lukasznowarkiewicz/DeafAlDer/imagesAndPhotos/altium/alarmClockScreen_pcb_bottom.JPG

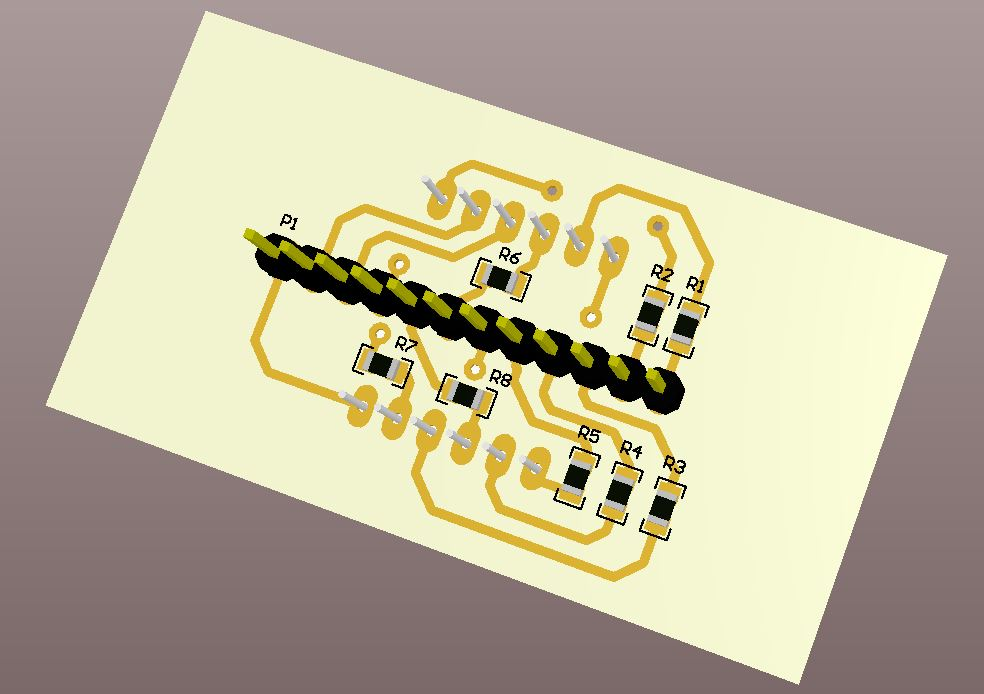
imagesAndPhotos/altium/alarmClockScreen_pcb_bottom.JPG
