lukasznowarkiewicz/DeafAlDer/imagesAndPhotos/altium/alarmClockScreen_pcb_top.JPG

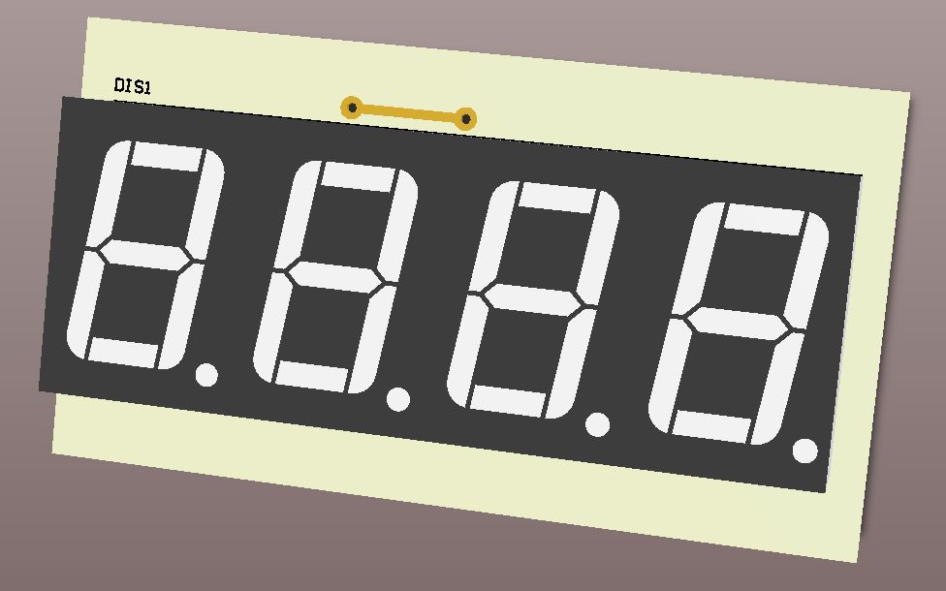
imagesAndPhotos/altium/alarmClockScreen_pcb_top.JPG
