lukasznowarkiewicz/DeafAlDer/imagesAndPhotos/altium/chadDetector_bottom.JPG

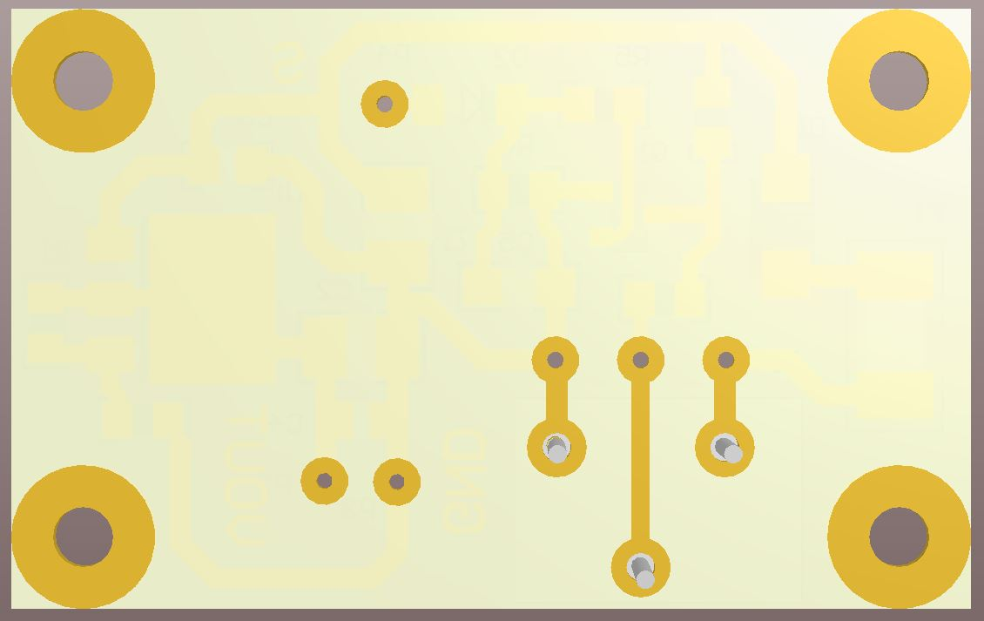
imagesAndPhotos/altium/chadDetector_bottom.JPG
