lukasznowarkiewicz/DeafAlDer/imagesAndPhotos/altium/chadDetector_pcb.JPG

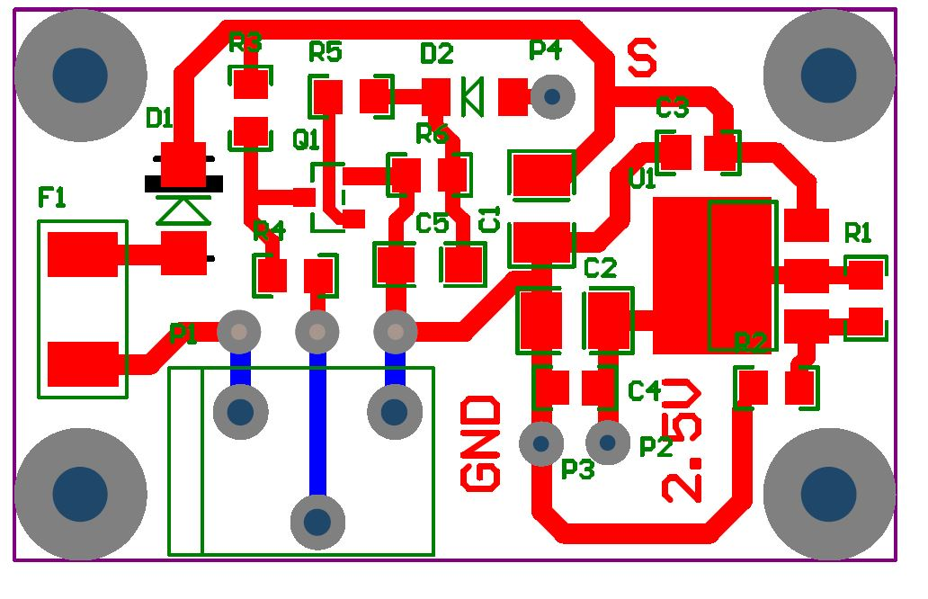
imagesAndPhotos/altium/chadDetector_pcb.JPG
