lukasznowarkiewicz/DeafAlDer/imagesAndPhotos/altium/chadDetector_top.JPG

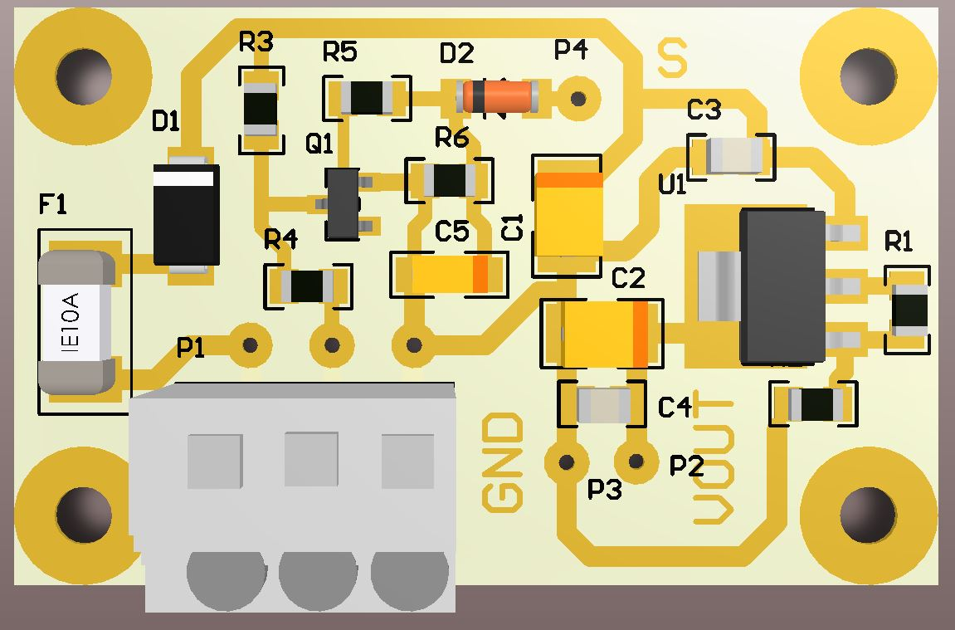
imagesAndPhotos/altium/chadDetector_top.JPG
