lukasznowarkiewicz/DeafAlDer/imagesAndPhotos/altium/ringingPhoneDetector_bottom.JPG

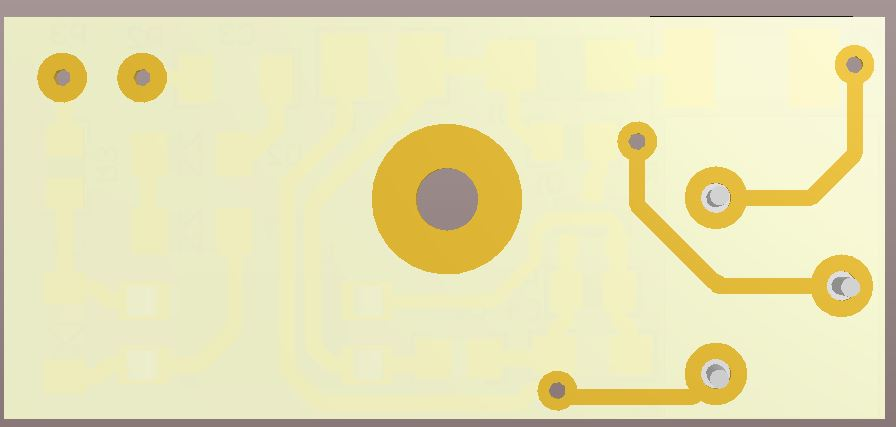
imagesAndPhotos/altium/ringingPhoneDetector_bottom.JPG
