lukasznowarkiewicz/DeafAlDer/imagesAndPhotos/altium/ringingPhoneDetector_pcb.JPG

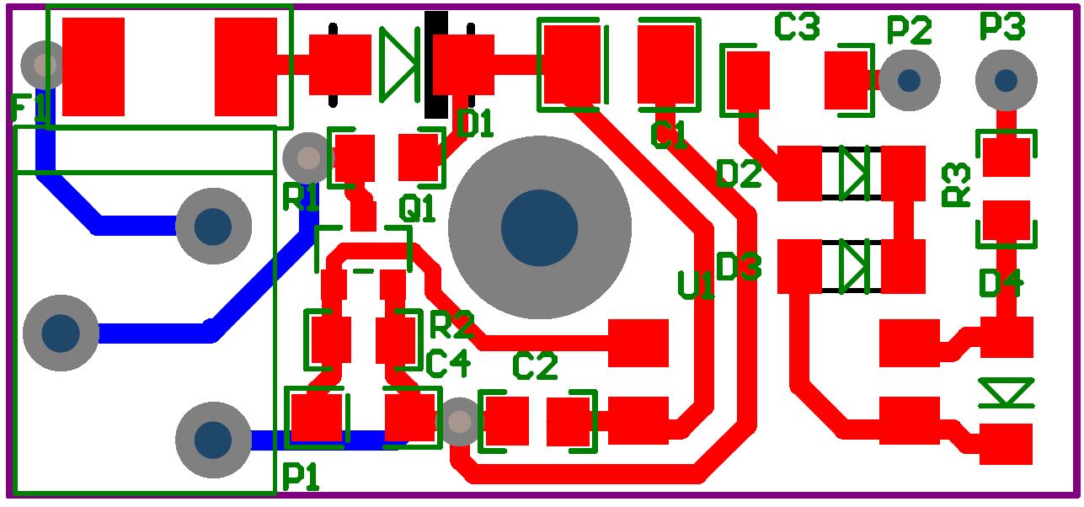
imagesAndPhotos/altium/ringingPhoneDetector_pcb.JPG
