lukasznowarkiewicz/DeafAlDer/imagesAndPhotos/altium/ringingPhoneDetector_sch.JPG

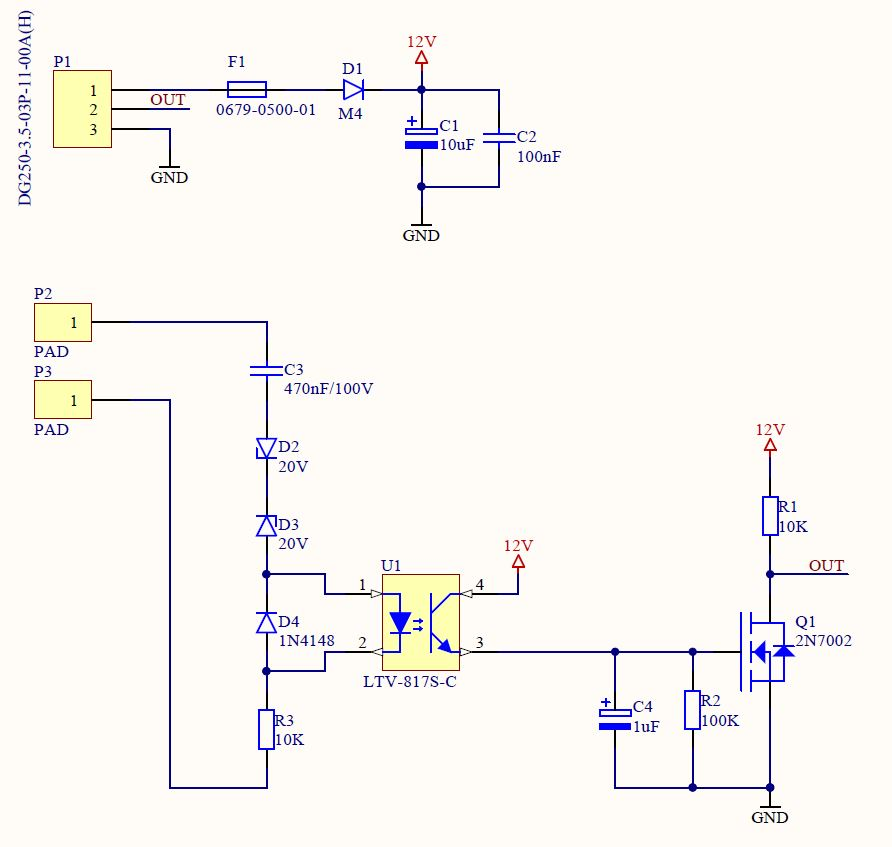
imagesAndPhotos/altium/ringingPhoneDetector_sch.JPG
