lukasznowarkiewicz/DeafAlDer/imagesAndPhotos/altium/ringingPhoneDetector_top.JPG

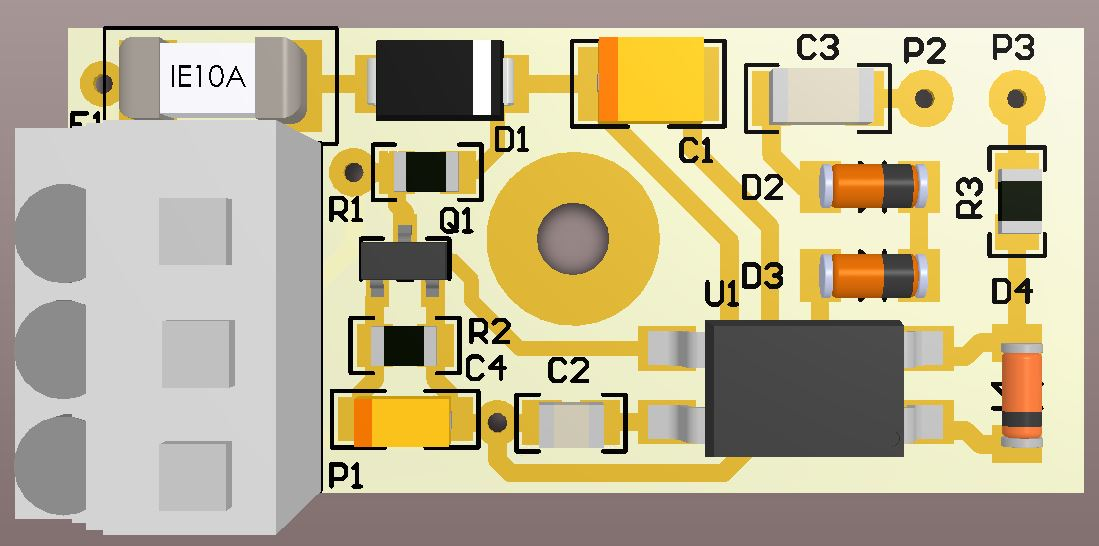
imagesAndPhotos/altium/ringingPhoneDetector_top.JPG
