lukasznowarkiewicz/DeafAlDer/imagesAndPhotos/altium/timer_bottom.JPG

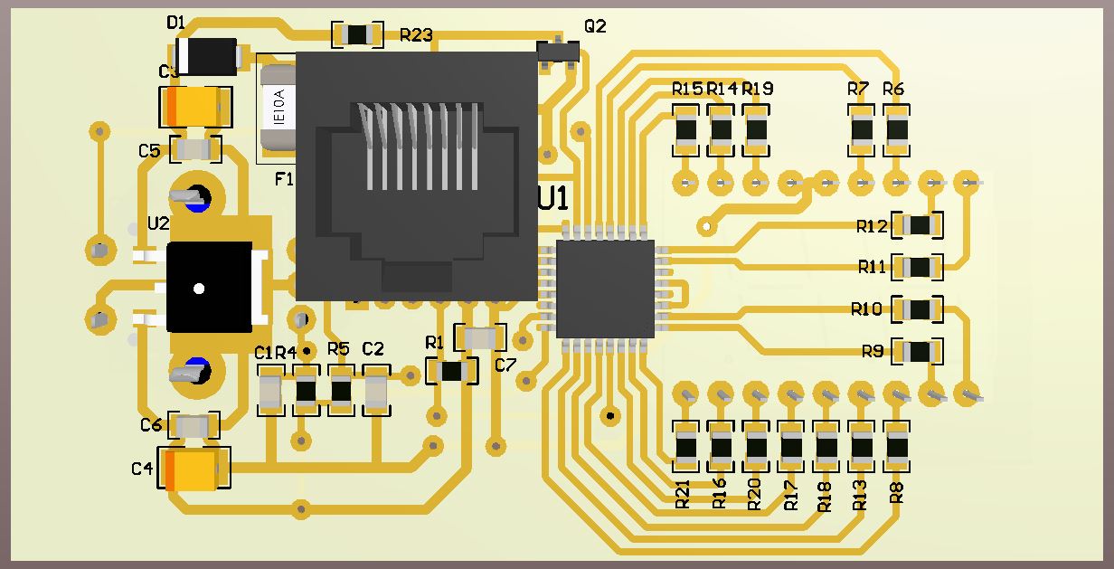
imagesAndPhotos/altium/timer_bottom.JPG
