lukasznowarkiewicz/DeafAlDer/imagesAndPhotos/doorbell1.JPG

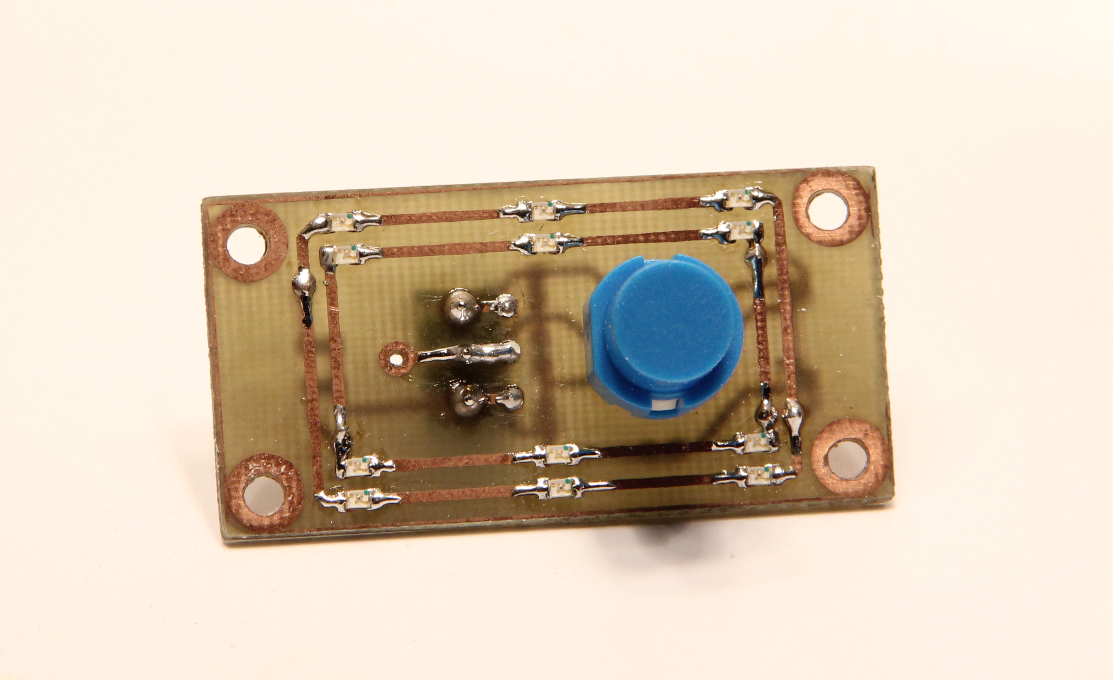
imagesAndPhotos/doorbell1.JPG
