lukasznowarkiewicz/DeafAlDer/imagesAndPhotos/doorbell2.JPG

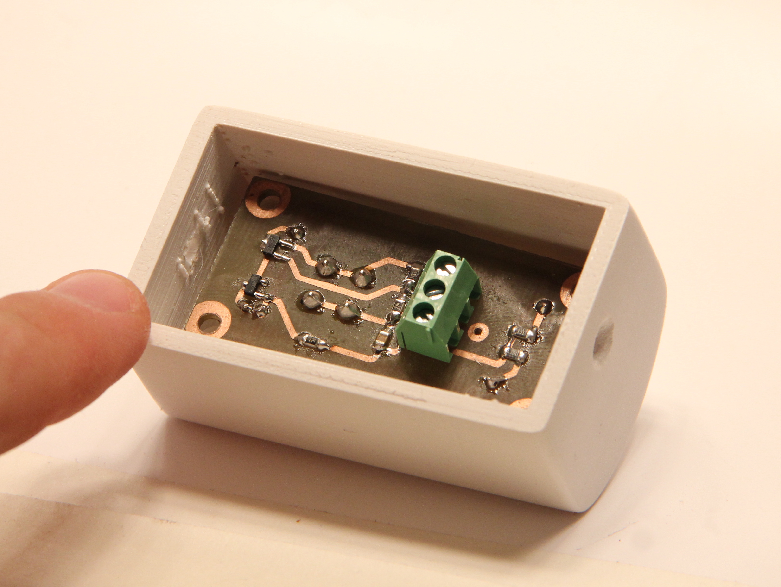
imagesAndPhotos/doorbell2.JPG
