lukasznowarkiewicz/DeafAlDer/imagesAndPhotos/doorbell3.JPG

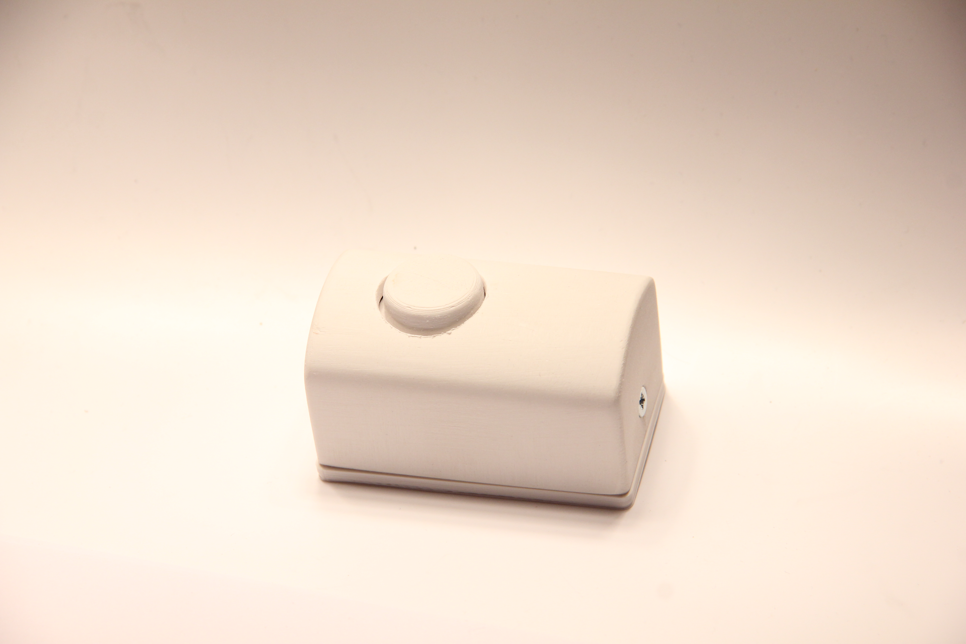
imagesAndPhotos/doorbell3.JPG
