lukasznowarkiewicz/DeafAlDer/imagesAndPhotos/PCB_preparation_3.JPG

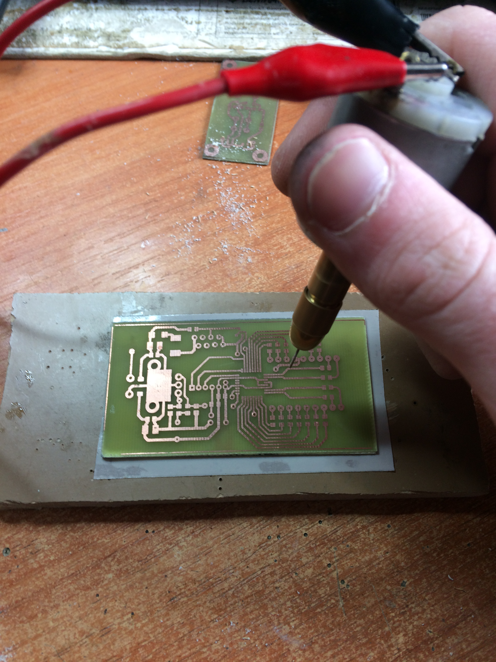
imagesAndPhotos/PCB_preparation_3.JPG
