lukasznowarkiewicz/DeafAlDer/imagesAndPhotos/PCB_preparation_4.JPG

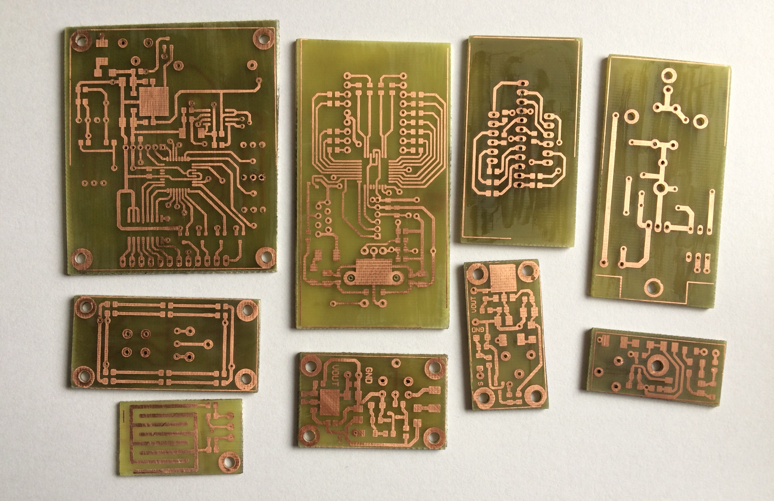
imagesAndPhotos/PCB_preparation_4.JPG
