lukasznowarkiewicz/DeafAlDer/imagesAndPhotos/smokeDetector.JPG

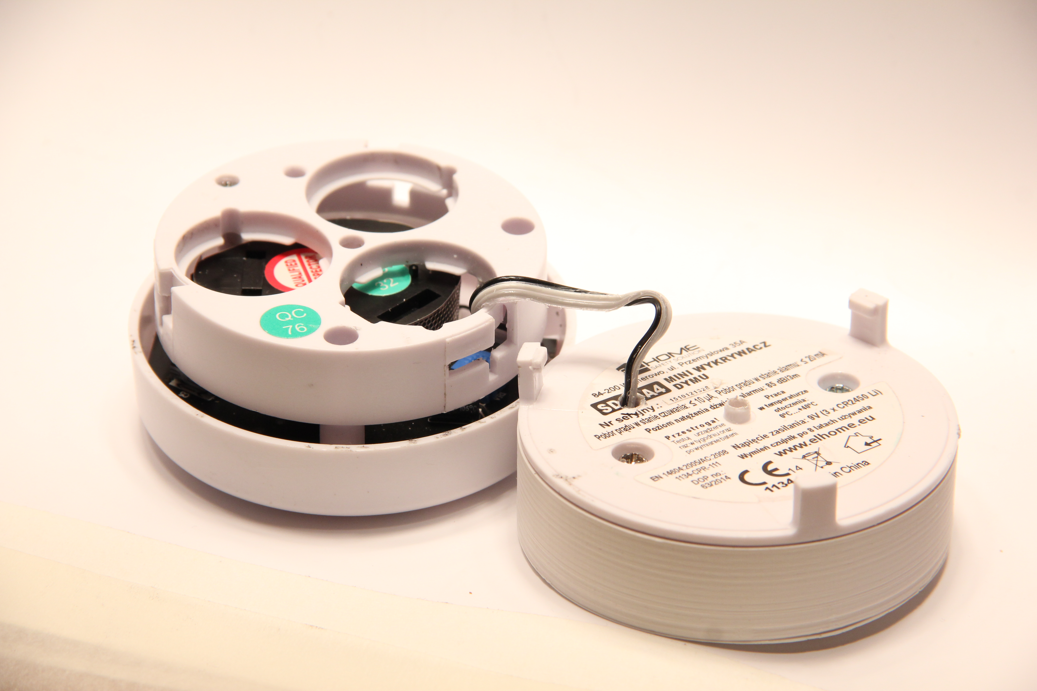
imagesAndPhotos/smokeDetector.JPG
