lukasznowarkiewicz/DeafAlDer/imagesAndPhotos/timer1.JPG

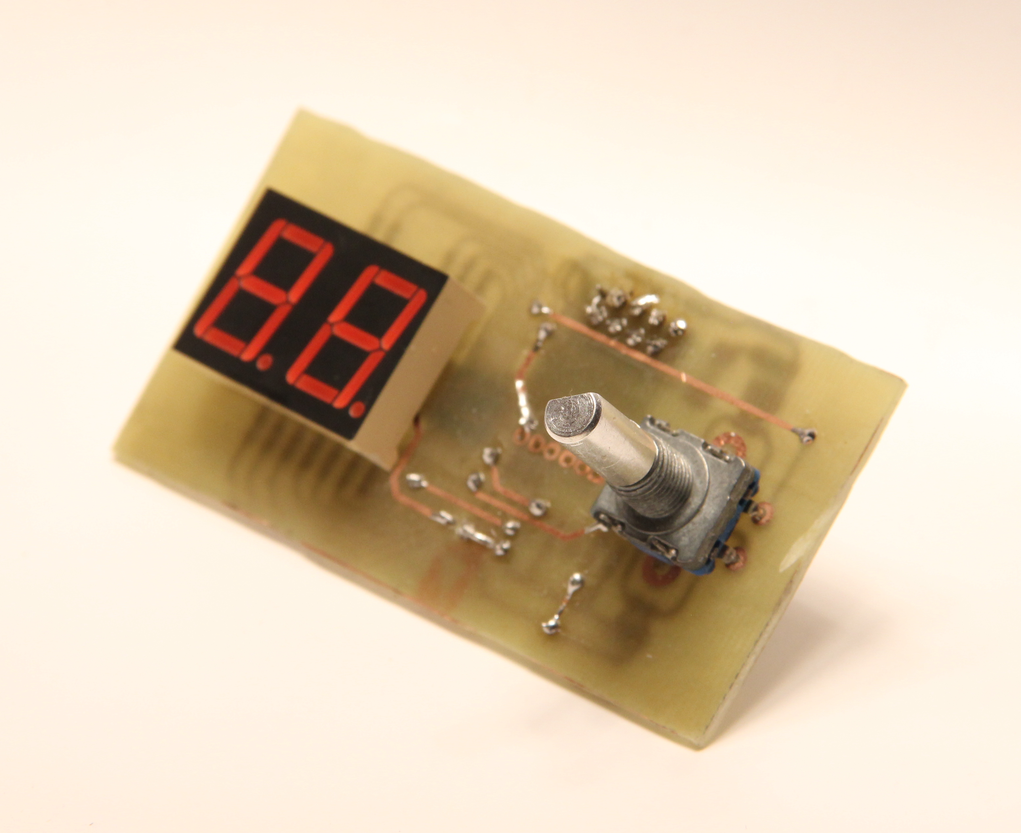
imagesAndPhotos/timer1.JPG
