lukasznowarkiewicz/DeafAlDer/imagesAndPhotos/trophy.JPG

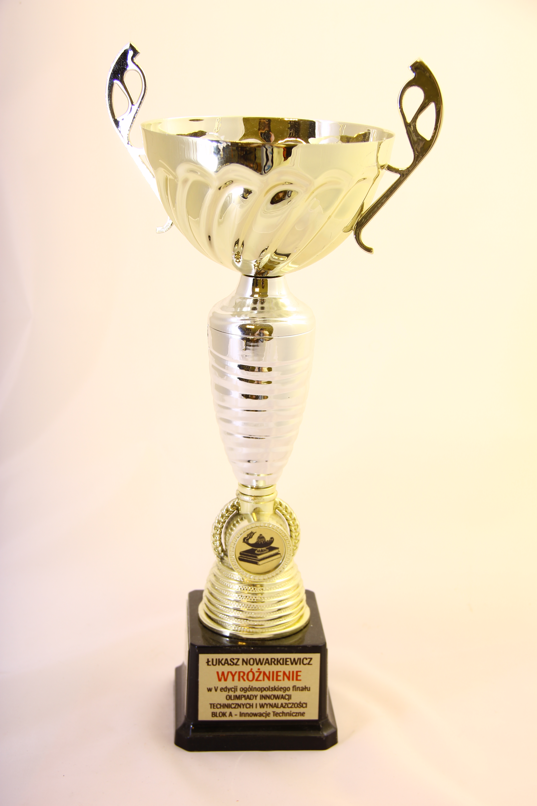
imagesAndPhotos/trophy.JPG
