lukasznowarkiewicz/DeafAlDer/hardware-mechanical/timer/obudowa - timer- back V2.stl

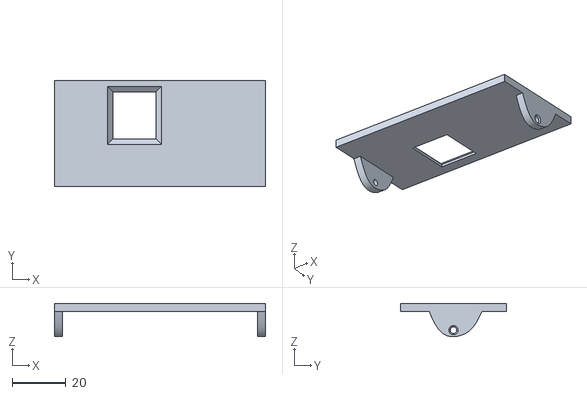
[picture p72: CAD file, 2024-03-28]
hardware-mechanical/timer/obudowa - timer- back V2.stl
78.5 x 39.5 x 12.4
