lukasznowarkiewicz/DeafAlDer/hardware-mechanical/alarmClock/obudowa - budzik v7 plexi.stl

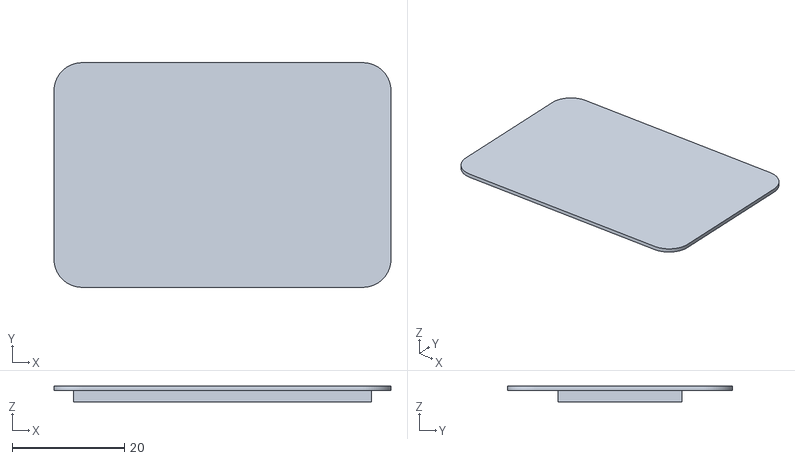
[picture p73: CAD file, 2024-03-28]
hardware-mechanical/alarmClock/obudowa - budzik v7 plexi.stl
60.0 x 40.0 x 2.80
