lukasznowarkiewicz/DeafAlDer/hardware-mechanical/doorbell/guzik.stl

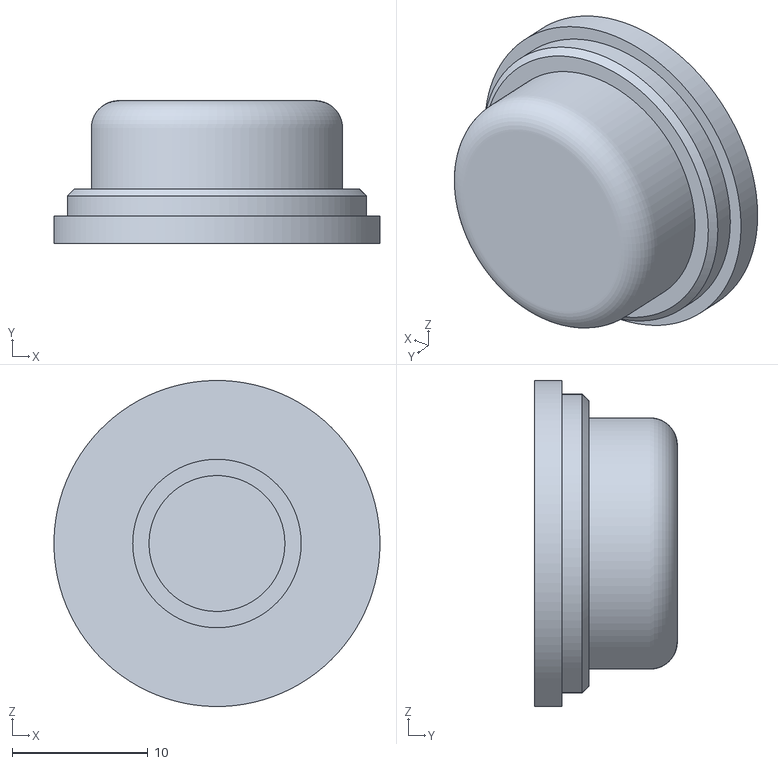
[picture p74: CAD file, 2024-03-28]
hardware-mechanical/doorbell/guzik.stl
24.0 x 10.5 x 24.0
