lukasznowarkiewicz/DeafAlDer/hardware-mechanical/namePlate/tabliczka tworcy i opiekun boki skrzynki.stl

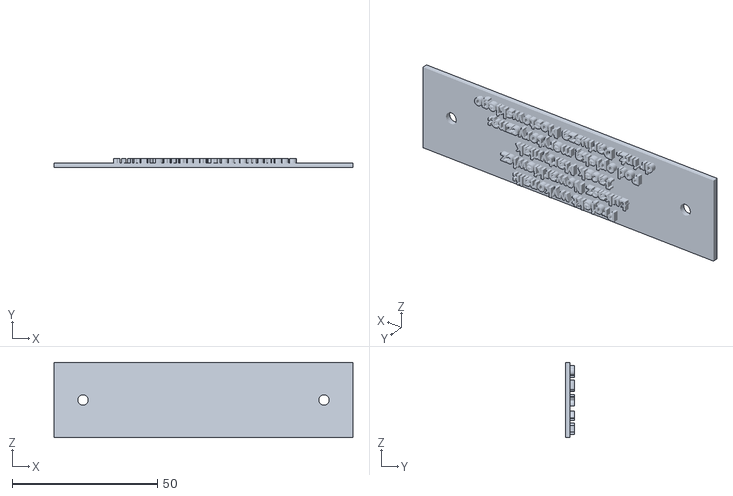
[picture p75: CAD file, 2024-03-28]
hardware-mechanical/namePlate/tabliczka tworcy i opiekun boki skrzynki.stl
103.0 x 3.20 x 26.0
