lukasznowarkiewicz/DeafAlDer/hardware-mechanical/timer/wysw trans v2.stl

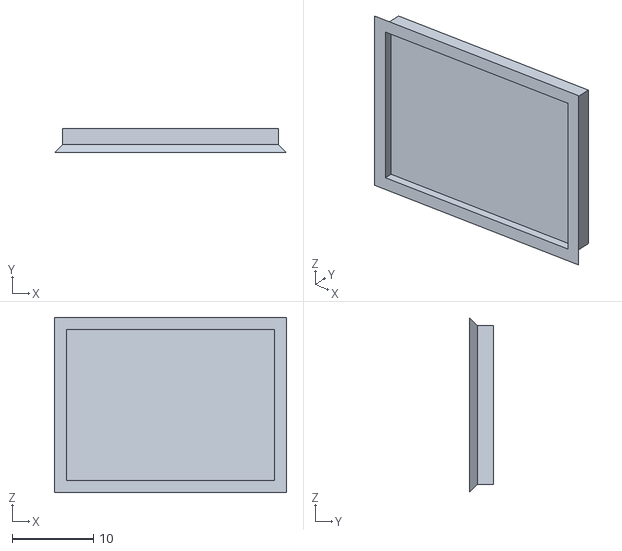
[picture p76: CAD file, 2024-03-28]
hardware-mechanical/timer/wysw trans v2.stl
28.6 x 3.00 x 21.6
