lukasznowarkiewicz/DeafAlDer/hardware-mechanical/doorbell/obudowa - dzwonek- tyl mocowanie do sciany.stl

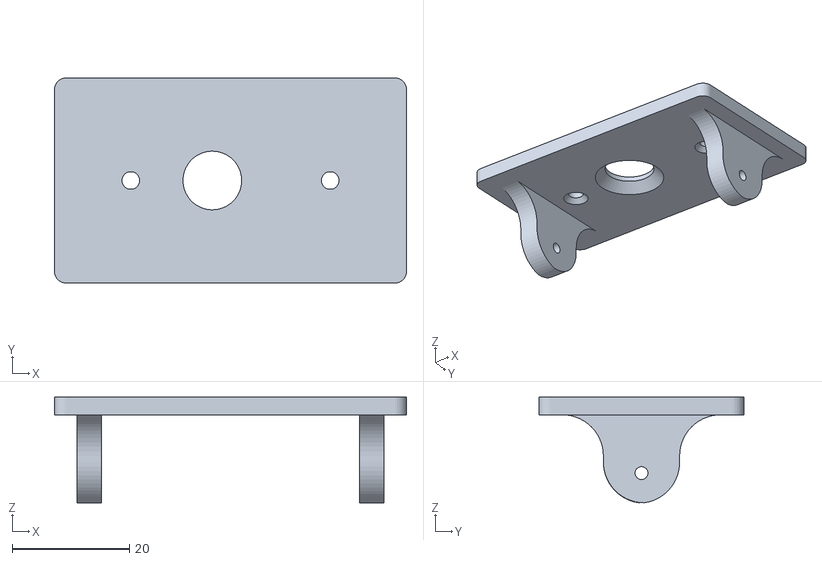
[picture p77: CAD file, 2024-03-28]
hardware-mechanical/doorbell/obudowa - dzwonek- tyl mocowanie do sciany.stl
60.0 x 35.0 x 18.0
