lukasznowarkiewicz/DeafAlDer/hardware-mechanical/namePlate/tabliczka z autorami i opiekunem na przod 170 x 50.stl

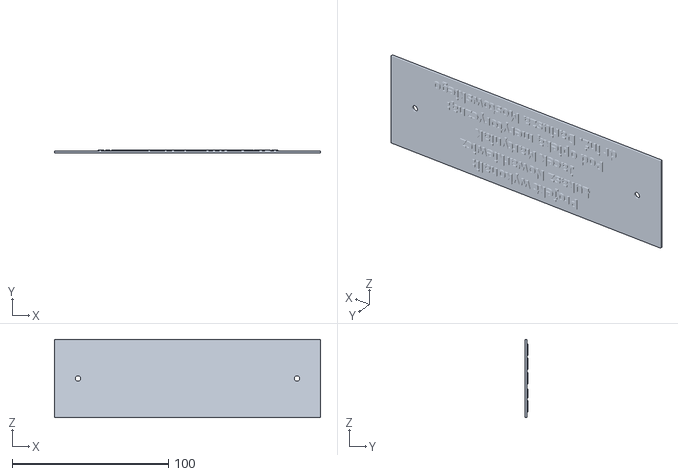
[picture p78: CAD file, 2024-03-28]
hardware-mechanical/namePlate/tabliczka z autorami i opiekunem na przod 170 x 50.stl
170.0 x 2.00 x 50.0
