lukasznowarkiewicz/DeafAlDer/hardware-mechanical/alarmClock/obudowa - budzik v5 dol dol.stl

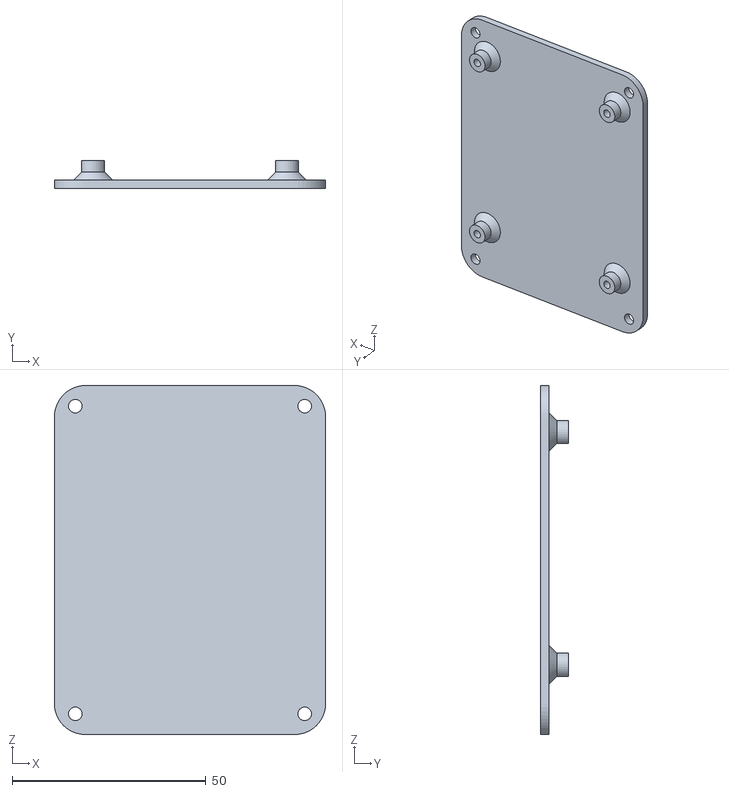
[picture p79: CAD file, 2024-03-28]
hardware-mechanical/alarmClock/obudowa - budzik v5 dol dol.stl
70.0 x 7.20 x 90.0
