lukasznowarkiewicz/DeafAlDer/hardware-mechanical/doorbell/obudowa - dzwonek - front.stl

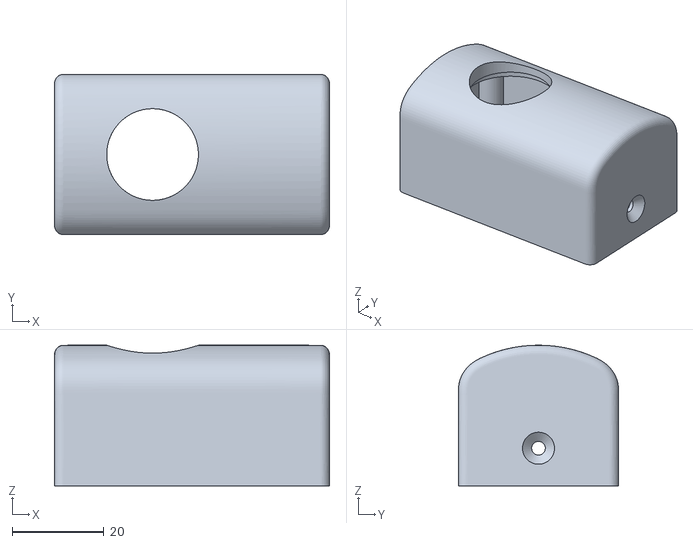
[picture p80: CAD file, 2024-03-28]
hardware-mechanical/doorbell/obudowa - dzwonek - front.stl
60.0 x 35.0 x 30.7
