lukasznowarkiewicz/DeafAlDer/hardware-mechanical/namePlate/logo na skrzynke z zewa.stl

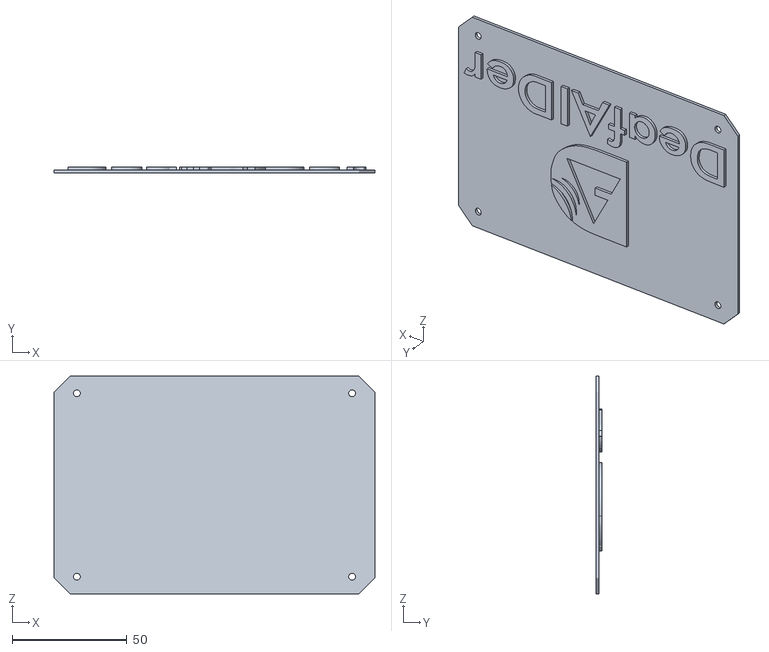
[picture p81: CAD file, 2024-03-28]
hardware-mechanical/namePlate/logo na skrzynke z zewa.stl
140.0 x 2.40 x 95.0
