lukasznowarkiewicz/DeafAlDer/hardware-mechanical/timer/wysw trans.stl

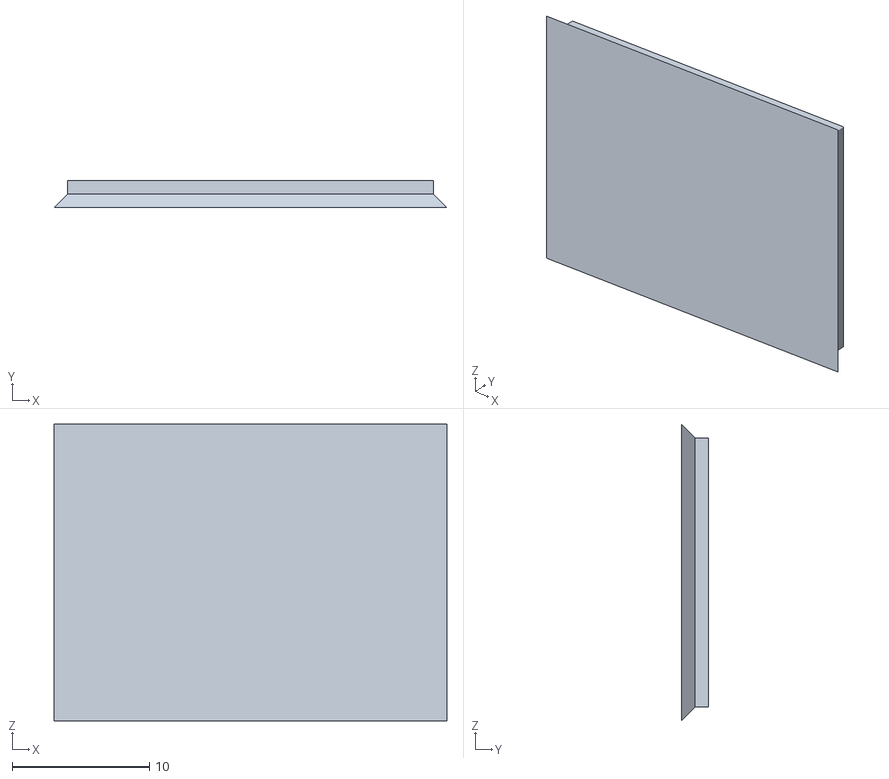
[picture p82: CAD file, 2024-03-28]
hardware-mechanical/timer/wysw trans.stl
28.6 x 2.00 x 21.6
