lukasznowarkiewicz/DeafAlDer/hardware-mechanical/alarmClock/obudowa - budzik v5 dol.stl

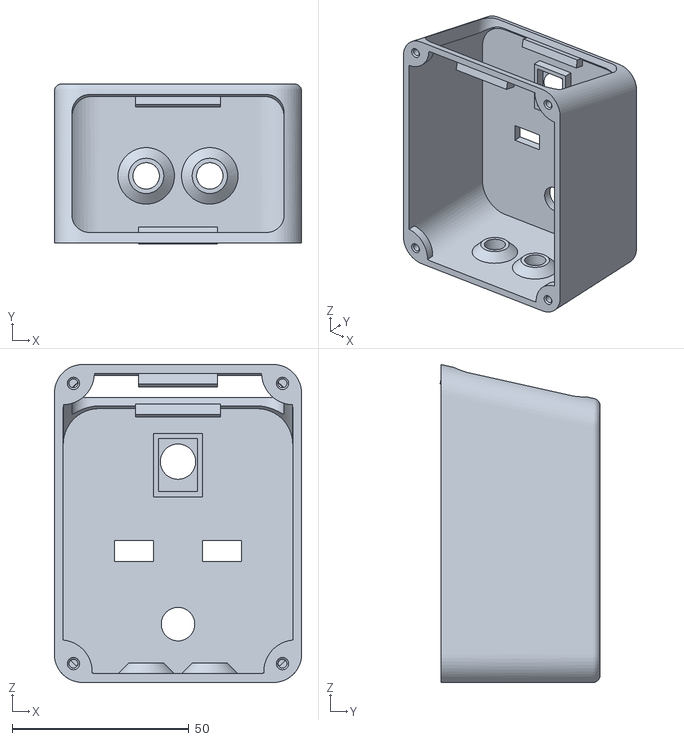
[picture p83: CAD file, 2024-03-28]
hardware-mechanical/alarmClock/obudowa - budzik v5 dol.stl
70.0 x 45.3 x 90.0
