lukasznowarkiewicz/DeafAlDer/hardware-mechanical/timer/obudowa - timer- back.stl

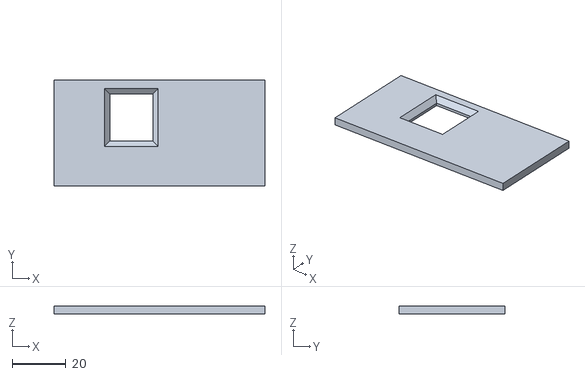
[picture p84: CAD file, 2024-03-28]
hardware-mechanical/timer/obudowa - timer- back.stl
78.5 x 39.5 x 3.00
