lukasznowarkiewicz/DeafAlDer/imagesAndPhotos/alarmClockEnclosureIn3dPrinter.JPG

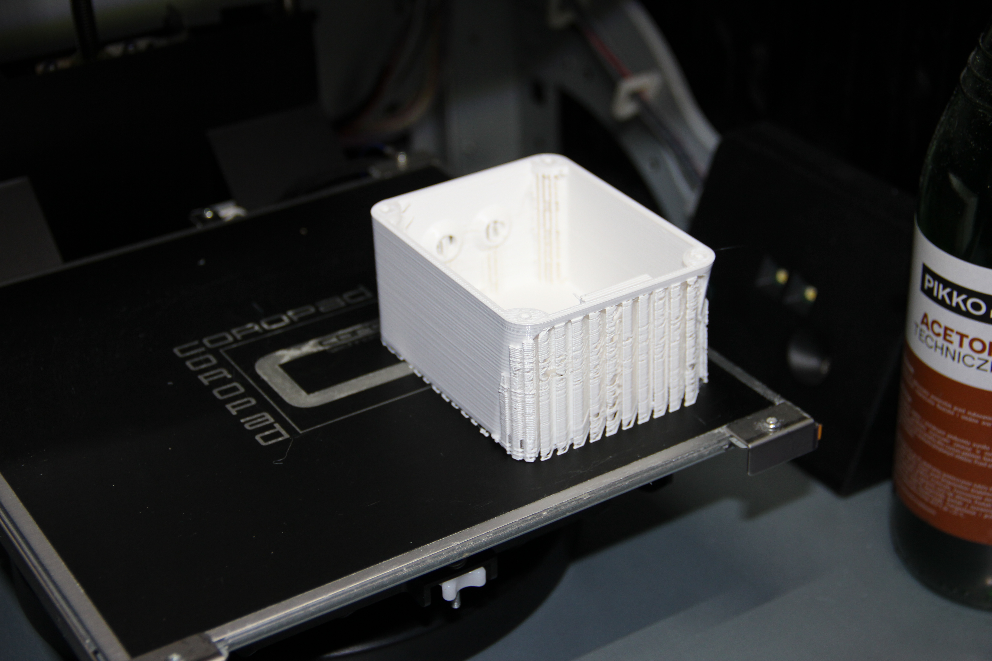
imagesAndPhotos/alarmClockEnclosureIn3dPrinter.JPG
