lukasznowarkiewicz/DeafAlDer/hardware-electronics/chadDetector/test points.jpg

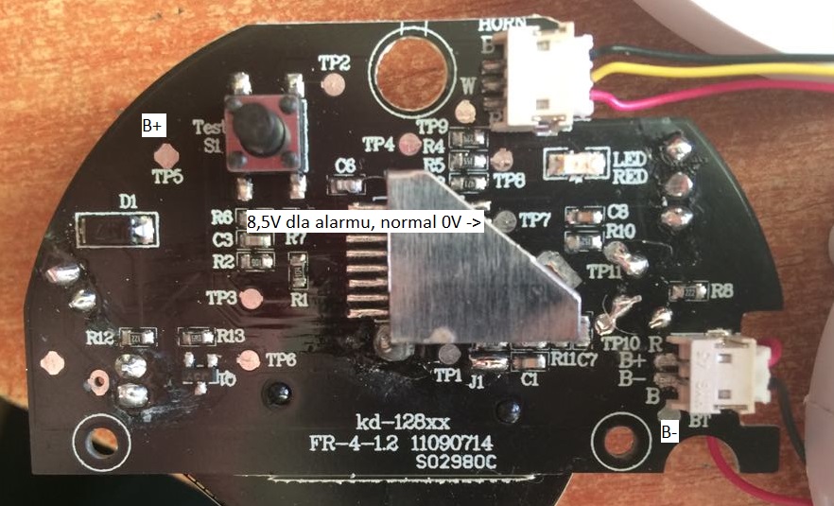
hardware-electronics/chadDetector/test points.jpg
